eggfly/pico-mac-nano/tft_2p_daxian.c

// 大显 480x640 竖屏2.0寸 TFT 屏幕

/* Functions to output to 2.0" 480x640 (Portrait) SPI & RBG565 TFT panel:
 *
 * Copyright 2025 Nick Gillard
 *
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
 * THE SOFTWARE IS PROVIDED "AS IS", WITHOUT WARRANTY OF ANY KIND,
 * EXPRESS OR IMPLIED, INCLUDING BUT NOT LIMITED TO THE WARRANTIES OF
 * MERCHANTABILITY, FITNESS FOR A PARTICULAR PURPOSE AND
 * NONINFRINGEMENT. IN NO EVENT SHALL THE AUTHORS OR COPYRIGHT HOLDERS
 * BE LIABLE FOR ANY CLAIM, DAMAGES OR OTHER LIABILITY, WHETHER IN AN
 * ACTION OF CONTRACT, TORT OR OTHERWISE, ARISING FROM, OUT OF OR IN
 * CONNECTION WITH THE SOFTWARE OR THE USE OR OTHER DEALINGS IN THE
 * SOFTWARE.
 */

#include <stdio.h>
#include <inttypes.h>
#include <string.h>
#include "pico/time.h"
#include "hardware/clocks.h"
#include "hardware/gpio.h"
#include "hw.h"
#include "ws2812.h" /* Needed for neo-pixel LED */
#include "tft_2p.h"

// TFT SPI Write command
static void tft_write_com(unsigned char comm) {
	static int i;

    put_pixel_red(1);
    gpio_put(TFT_SPI_CS, 0); // Chip select enabled
    gpio_put(TFT_SPI_MOSI, 0);
    gpio_put(TFT_SPI_CLK, 0);
    sleep_us(TFT_SPI_PAUSE);
    gpio_put(TFT_SPI_CLK, 1);

    for(i=0;i<8;i++) {
        if(comm & 0x80) {
            gpio_put(TFT_SPI_MOSI, 1);
        } else {
            gpio_put(TFT_SPI_MOSI, 0);
        }
        gpio_put(TFT_SPI_CLK, 0);
        sleep_us(TFT_SPI_PAUSE);
        gpio_put(TFT_SPI_CLK, 1);
        comm<<=1;
    }
    gpio_put(TFT_SPI_CS, 1); // Chip select disabled
    put_pixel_red(0);
}

// SPI Write Data
static void tft_write_dat(unsigned char datt) {
    static int j;

    put_pixel_red(1);
    gpio_put(TFT_SPI_CS, 0); // Chip select enabled

    // First send a 1 for bit 9
    gpio_put(TFT_SPI_MOSI, 1);
    gpio_put(TFT_SPI_CLK, 0);
    sleep_us(TFT_SPI_PAUSE);
    gpio_put(TFT_SPI_CLK, 1);

    for(j=0;j<8;j++) {
        if(datt & 0x80) { // true if left most bit is a 1. Bitwisecompare of datt with binary 10000000
            gpio_put(TFT_SPI_MOSI, 1);
        } else {
            gpio_put(TFT_SPI_MOSI, 0);
        }
        gpio_put(TFT_SPI_CLK, 0);
        sleep_us(TFT_SPI_PAUSE);
        gpio_put(TFT_SPI_CLK, 1);
        datt<<=1; // Bit shift left 1
    }

    gpio_put(TFT_SPI_CS, 1); // Chip select disabled
    put_pixel_red(0);
}

void tft_init() {
    
    gpio_init(TFT_RESET);
    gpio_set_dir(TFT_RESET, GPIO_OUT);

    // Initialize SPI pins
    gpio_init(TFT_SPI_CS);
    gpio_set_dir(TFT_SPI_CS, GPIO_OUT);
    gpio_put(TFT_SPI_CS, 1);// Initialize TFT CS pin high
    gpio_init(TFT_SPI_CLK);
    gpio_set_dir(TFT_SPI_CLK, GPIO_OUT);
    gpio_init(TFT_SPI_MOSI);
    gpio_set_dir(TFT_SPI_MOSI, GPIO_OUT);

    // sleep_ms(5);

    gpio_put(TFT_RESET, 1); // Set TFT Reset pin high
    sleep_ms(1);
    gpio_put(TFT_RESET, 0);  // Set TFT Reset pin low
    sleep_ms(1);
    gpio_put(TFT_RESET, 1);  // Set TFT Reset pin high
    sleep_ms(1);

    tft_write_com(0xFF);    // Command2 BKx Selection - 12.3.1
    tft_write_dat(0x77);    // 
    tft_write_dat(0x01);
    tft_write_dat(0x00);
    tft_write_dat(0x00);
    tft_write_dat(0x13);

    tft_write_com(0xEF);    // ??
    tft_write_dat(0x08);

    tft_write_com(0xFF);    // Command2 BKx Selection - 12.3.1
    tft_write_dat(0x77);
    tft_write_dat(0x01);
    tft_write_dat(0x00);
    tft_write_dat(0x00);
    tft_write_dat(0x10);

    tft_write_com(0xC0);    // Command 2 BK0: LNESET (C0h/C000h): Display Line Setting - 12.3.2.7
    tft_write_dat(0x4F);
    tft_write_dat(0x00);

    tft_write_com(0xC1);    // Command 2 BK0: PORCTRL (C1h/C100h):Porch Control - 12.3.2.8
    tft_write_dat(0x11);    // VBP[7:0]: Back-Porch Vertical line setting for display.
    tft_write_dat(0x0C);    // VFP[7:0]: Front-Porch Vertical line setting for display.

    tft_write_com(0xC2);    // Command 2 BK0: INVSET (C2h/C200h):Inversion selection & Frame Rate Control - 12.3.2.9
    tft_write_dat(0x07);
    tft_write_dat(0x0A);

    tft_write_com(0xC3);    // Command 2 BK0: RGBCTRL (C3h/C300h):RGB control - 12.3.2.10
    tft_write_dat(0x83);    // DE/HV - - - VSP HSP DP EP : VS Polarity, HS Pol, Dot/pixel Clk Pol, Enable Pin Pol. 0x83 = 10000011 VS & HS active when low, DP input on falling edge, EP Data written when enable is 0.
    tft_write_dat(0x33);    // HBP_HVRGB[7:0]. 0x33 = 51
    tft_write_dat(0x1b);    // VBP_HVRGB[7:0]. 0x1b = 27


    tft_write_com(0xCC);    // ??
    tft_write_dat(0x10);

    tft_write_com(0xB0);    // Command 2 BK0: PVGAMCTRL (B0h/B000h): Positive Voltage Gamma Control - 12.3.2.1
    tft_write_dat(0x00);
    tft_write_dat(0x0F);
    tft_write_dat(0x18);
    tft_write_dat(0x0D);
    tft_write_dat(0x12);
    tft_write_dat(0x07);
    tft_write_dat(0x05);
    tft_write_dat(0x08);
    tft_write_dat(0x07);
    tft_write_dat(0x21);
    tft_write_dat(0x03);
    tft_write_dat(0x10);
    tft_write_dat(0x0F);
    tft_write_dat(0x26);
    tft_write_dat(0x2F);
    tft_write_dat(0x1F);

    tft_write_com(0xB1);    // NVGAMCTRL (B1h/B100h): Negative Voltage Gamma Control - 12.3.2.2
    tft_write_dat(0x00);
    tft_write_dat(0x1B);
    tft_write_dat(0x20);
    tft_write_dat(0x0C);
    tft_write_dat(0x0E);
    tft_write_dat(0x03);
    tft_write_dat(0x08);
    tft_write_dat(0x08);
    tft_write_dat(0x08);
    tft_write_dat(0x22);
    tft_write_dat(0x05);
    tft_write_dat(0x11);
    tft_write_dat(0x0F);
    tft_write_dat(0x2A);
    tft_write_dat(0x32);
    tft_write_dat(0x1F);

    tft_write_com(0xFF);    // Command2 BKx Selection - 12.3.1
    tft_write_dat(0x77);
    tft_write_dat(0x01);
    tft_write_dat(0x00);
    tft_write_dat(0x00);
    tft_write_dat(0x11);

    tft_write_com(0xB0);    // Command 2 BK0: PVGAMCTRL (B0h/B000h): Positive Voltage Gamma Control - 12.3.2.1
    tft_write_dat(0x35);

    tft_write_com(0xB1);    // NVGAMCTRL (B1h/B100h): Negative Voltage Gamma Control - 12.3.2.2
    tft_write_dat(0x6a);

    tft_write_com(0xB2);    // VGHSS (B2h/B200h):VGH Voltage setting - 12.3.3.3
    tft_write_dat(0x81);

    tft_write_com(0xB3);    // TESTCMD (B3h/B300h):TEST Command Setting - 12.3.3.4
    tft_write_dat(0x80);

    tft_write_com(0xB5);    // VGLS (B5h/B500h):VGL Voltage setting - 12.3.3.5
    tft_write_dat(0x4E);

    tft_write_com(0xB7);    // PWCTRL1 (B7h/B700h):Power Control 1 - 12.3.3.6
    tft_write_dat(0x85);

    tft_write_com(0xB8);    // Command 2 BK0: DGMEN (B8h/B800h): Digital Gamma Enable - 12.3.2.3
    tft_write_dat(0x21);

    tft_write_com(0xC0);    // Command 2 BK0: LNESET (C0h/C000h): Display Line Setting - 12.3.2.7
    tft_write_dat(0x09);

    tft_write_com(0xC1);    // Command 2 BK0: PORCTRL (C1h/C100h):Porch Control - 12.3.2.8
    tft_write_dat(0x78);

    tft_write_com(0xC2);    // Command 2 BK0: INVSET (C2h/C200h):Inversion selection & Frame Rate Control - 12.3.2.9
    tft_write_dat(0x78);

    tft_write_com(0xD0);    // MIPISET1 (D0h/D000h):MIPI Setting 1 - 12.3.3.14
    tft_write_dat(0x88);

    tft_write_com(0xE0);    // SECTRL (E0h/E000h):Sunlight Readable Enhancement - 12.3.2.16
    tft_write_dat(0x00);
    tft_write_dat(0xA0);
    tft_write_dat(0x02);

    tft_write_com(0xE1);    // NRCTRL (E1h/E100h):Noise Reduce Control - 12.3.2.17
    tft_write_dat(0x06);
    tft_write_dat(0xA0);
    tft_write_dat(0x08);
    tft_write_dat(0xA0);
    tft_write_dat(0x05);
    tft_write_dat(0xA0);
    tft_write_dat(0x07);
    tft_write_dat(0xA0);
    tft_write_dat(0x00);
    tft_write_dat(0x44);
    tft_write_dat(0x44);

    tft_write_com(0xE2);    // SECTRL (E2h/E200h):Sharpness Control - 12.3.2.18
    tft_write_dat(0x20);
    tft_write_dat(0x20);
    tft_write_dat(0x40);
    tft_write_dat(0x40);
    tft_write_dat(0x96);
    tft_write_dat(0xA0);
    tft_write_dat(0x00);
    tft_write_dat(0x00);
    tft_write_dat(0x96);
    tft_write_dat(0xA0);
    tft_write_dat(0x00);
    tft_write_dat(0x00);
    tft_write_dat(0x00);

    tft_write_com(0xE3);    // CCCTRL (E3h/E300h):Color Calibration Control - 12.3.2.19
    tft_write_dat(0x00);
    tft_write_dat(0x00);
    tft_write_dat(0x22);
    tft_write_dat(0x22);

    tft_write_com(0xE4);    // SKCTRL (E4h/E400h):Skin Tone Preservation Control - 12.3.2.20
    tft_write_dat(0x44);
    tft_write_dat(0x44);

    tft_write_com(0xE5);    // ??
    tft_write_dat(0x0E);
    tft_write_dat(0x97);
    tft_write_dat(0x10);
    tft_write_dat(0xA0);
    tft_write_dat(0x10);
    tft_write_dat(0x99);
    tft_write_dat(0x10);
    tft_write_dat(0xA0);
    tft_write_dat(0x0A);
    tft_write_dat(0x93);
    tft_write_dat(0x10);
    tft_write_dat(0xA0);
    tft_write_dat(0x0C);
    tft_write_dat(0x95);
    tft_write_dat(0x10);
    tft_write_dat(0xA0);

    tft_write_com(0xE6);    // ??
    tft_write_dat(0x00);
    tft_write_dat(0x00);
    tft_write_dat(0x22);
    tft_write_dat(0x22);

    tft_write_com(0xE7);    // ??
    tft_write_dat(0x44);
    tft_write_dat(0x44);

    tft_write_com(0xE8);    // ??
    tft_write_dat(0x0D);
    tft_write_dat(0x96);
    tft_write_dat(0x10);
    tft_write_dat(0xA0);
    tft_write_dat(0x0F);
    tft_write_dat(0x98);
    tft_write_dat(0x10);
    tft_write_dat(0xA0);
    tft_write_dat(0x09);
    tft_write_dat(0x92);
    tft_write_dat(0x10);
    tft_write_dat(0xA0);
    tft_write_dat(0x0B);
    tft_write_dat(0x94);
    tft_write_dat(0x10);
    tft_write_dat(0xA0);

    tft_write_com(0xEB);    // ??
    tft_write_dat(0x00);
    tft_write_dat(0x01);
    tft_write_dat(0x4E);
    tft_write_dat(0x4E);
    tft_write_dat(0x44);
    tft_write_dat(0x88);
    tft_write_dat(0x40);

    tft_write_com(0xEC);    // ??
    tft_write_dat(0x78);
    tft_write_dat(0x00);

    tft_write_com(0xED);    // ??
    tft_write_dat(0xFF);
    tft_write_dat(0xFA);
    tft_write_dat(0x2F);
    tft_write_dat(0x89);
    tft_write_dat(0x76);
    tft_write_dat(0x54);
    tft_write_dat(0x01);
    tft_write_dat(0xFF);
    tft_write_dat(0xFF);
    tft_write_dat(0x10);
    tft_write_dat(0x45);
    tft_write_dat(0x67);
    tft_write_dat(0x98);
    tft_write_dat(0xF2);
    tft_write_dat(0xAF);
    tft_write_dat(0xFF);

    tft_write_com(0xEF);    // ??
    tft_write_dat(0x08);
    tft_write_dat(0x08);
    tft_write_dat(0x08);
    tft_write_dat(0x45);
    tft_write_dat(0x3F);
    tft_write_dat(0x54);

    tft_write_com(0xFF);    // Command2 BKx Selection - 12.3.1
    tft_write_dat(0x77);
    tft_write_dat(0x01);
    tft_write_dat(0x00);
    tft_write_dat(0x00);
    tft_write_dat(0x13);

    tft_write_com(0xE8);    // ??
    tft_write_dat(0x00);
    tft_write_dat(0x0E);


    tft_write_com(0xE8);    // ??
    tft_write_dat(0x00);
    tft_write_dat(0x0C);
    sleep_ms(10);

    tft_write_com(0xE8);    // ??
    tft_write_dat(0x00);
    tft_write_dat(0x00);

    tft_write_com(0xFF);    // Command2 BKx Selection - 12.3.1
    tft_write_dat(0x77);     
    tft_write_dat(0x01);
    tft_write_dat(0x00);
    tft_write_dat(0x00);
    tft_write_dat(0x00);

    tft_write_com(0x3A);    // COLMOD (3Ah/3A00h): Interface Pixel Format - 12.2.30
    tft_write_dat(0x55);    // 0x55   RGB565   //0x77  RGB888

    tft_write_com(0x29);    // DISPON (29h/2900h): Display On - 12.2.24
    tft_write_dat(0x00);

    tft_write_com(0x11);    // SLPOUT (11h/1100h): Sleep Out - 12.2.15
 //   sleep_ms(120);

//   tft_write_com(0x23); // All pixels on (white)
 //   sleep_ms(120);
 //   tft_write_com(0x22); // All pixels off (black)
}
