eggfly/pico-mac-nano/data_sheets/D200C2409V0 480640 SPEC/FT6336.h

#ifndef __MSG2233_H_
#define __MSG2233_H_
#include "sys_nvic.h" 
#include "typedef.h" 

#define MSG_INT PBin(14)
#define MSG_RST PBout(15)


{
	TP_Stu_NoPress = 0,//初始值
	TP_Stu_Press = 1,//按下状态
	TP_Stu_DoPress = 2,//可以处理	
};


//初始化
void MSG2233Init(void);
//读取触摸点
U8  ReadTpPoint(void);


/***********************************************************************
* 函数名称    : TP_ComCountAdd
* 描述        : 通讯超时计数自加
* 输入形参    :
* 返回值      :
************************************************************************/
void TP_ComCountAdd(void);

/***********************************************************************
* 函数名称    : ReadTpComOutFlag
* 描述        : 通讯超时标识
* 输入形参    : 无
* 返回值      : 无
************************************************************************/
UINT16 ReadTpComOutFlag(void);
/***********************************************************************
* 函数名称    : ClearTpComOutFlag
* 描述        : 清除通讯超时标识
* 输入形参    : 无
* 返回值      : 无
************************************************************************/
void ClearTpComOutFlag(void);
/***********************************************************************
* 函数名称    : ReadTpPressStu
* 描述        : 读取Tp状态
* 输入形参    : 无
* 返回值      : 无
************************************************************************/
UINT8 ReadTpPressStu(void);
/***********************************************************************
* 函数名称    : SetTpPressStu
* 描述        : 设置按下状态
* 输入形参    : 无
* 返回值      : 无
************************************************************************/
void ClearTpPressStu(void);
/***********************************************************************
* 函数名称    : getTPPoint
* 描述        : 获取坐标值
* 输入形参    : 无
* 返回值      : 无
************************************************************************/
void getTPPoint(TP_POINT *point);
/***********************************************************************
* 函数名称    : TP_SpeedAdd
* 描述        : 速度计数自加
* 输入形参    :
* 返回值      :
************************************************************************/
void TP_SpeedAdd(void);

/***********************************************************************
* 函数名称    : getSpeedx
* 描述        : 获取x速度
* 输入形参    : 无
* 返回值      : 无
************************************************************************/
int getSpeedx(void);
/***********************************************************************
* 函数名称    : getSpeedy
* 描述        : 获取y速度
* 输入形参    : 无
* 返回值      : 无
************************************************************************/
int getSpeedy(void);
/***********************************************************************
* 函数名称    : ClearSpeed
* 描述        : 清空速度
* 输入形参    : 无
* 返回值      : 无
************************************************************************/
void ClearSpeed(void);
/***********************************************************************
* 函数名称    : getSpeedx
* 描述        : 获取x速度
* 输入形参    : 无
* 返回值      : 无
************************************************************************/
U16 getMaxSpeedy(void);
/***********************************************************************
* 函数名称    : getSpeedx
* 描述        : 获取x速度
* 输入形参    : 无
* 返回值      : 无
************************************************************************/
U8 getSmallSpeedx(void);
/***********************************************************************
* 函数名称    : getSpeedy
* 描述        : 获取y速度
* 输入形参    : 无
* 返回值      : 无
************************************************************************/
U8 getSmallSpeedy(void);
/***********************************************************************
* 函数名称    : getSpeedx
* 描述        : 获取x速度
* 输入形参    : 无
* 返回值      : 无
************************************************************************/
void ClearSmallSpeedx(void);
/***********************************************************************
* 函数名称    : getSpeedy
* 描述        : 获取y速度
* 输入形参    : 无
* 返回值      : 无
************************************************************************/
void ClearSmallSpeedy(void);
/***********************************************************************
* 函数名称    : DoSpeedY
* 描述        : 20ms执行一次每次降低50%
* 输入形参    : 无
* 返回值      : 无
************************************************************************/
int DoSpeedY(void);
/***********************************************************************
* 函数名称    : getOffSetSpeedy
* 描述        : 获取y速度差
* 输入形参    : 无
* 返回值      : 无
************************************************************************/
int getOffSetSpeedy(void);
/***********************************************************************
* 函数名称    : ReadSign_speedx
* 描述        : 
* 输入形参    : 无
* 返回值      : 无
************************************************************************/
UINT8  ReadSign_speedx(void);
/***********************************************************************
* 函数名称    : ReadSign_speedy
* 描述        : 
* 输入形参    : 无
* 返回值      : 无
************************************************************************/
UINT8  ReadSign_speedy(void);
/***********************************************************************
* 函数名称    : SetSlideEnable
* 描述        : 滑动允许区域
* 输入形参    : 无
* 返回值      : 无
************************************************************************/
void SetSlideEnable(YRECT Rect);

/***********************************************************************
* 函数名称    : GetEnaSlide
* 描述        : 获取滑动允许标志
* 输入形参    : 无
* 返回值      : 滑动允许标志
************************************************************************/
INT8U  GetEnaSlide(void);
/***********************************************************************
* 函数名称    : ClearEnaSlide
* 描述        : 清除滑动允许标志
* 输入形参    : 无
* 返回值      : 
************************************************************************/
void  ClearEnaSlide(void);

/***********************************************************************
* 函数名称    : CheckSlide
* 描述        : 判断滑动
* 输入形参    :
* 返回值      :
************************************************************************/
void TP_CheckSlide(void);
void SetSpeedy(I16 speed);
#endif
